ji1udd/VFO-Controller/Doc/Shop2906194(Not Available Now)_SwitchLid_info2.jpg

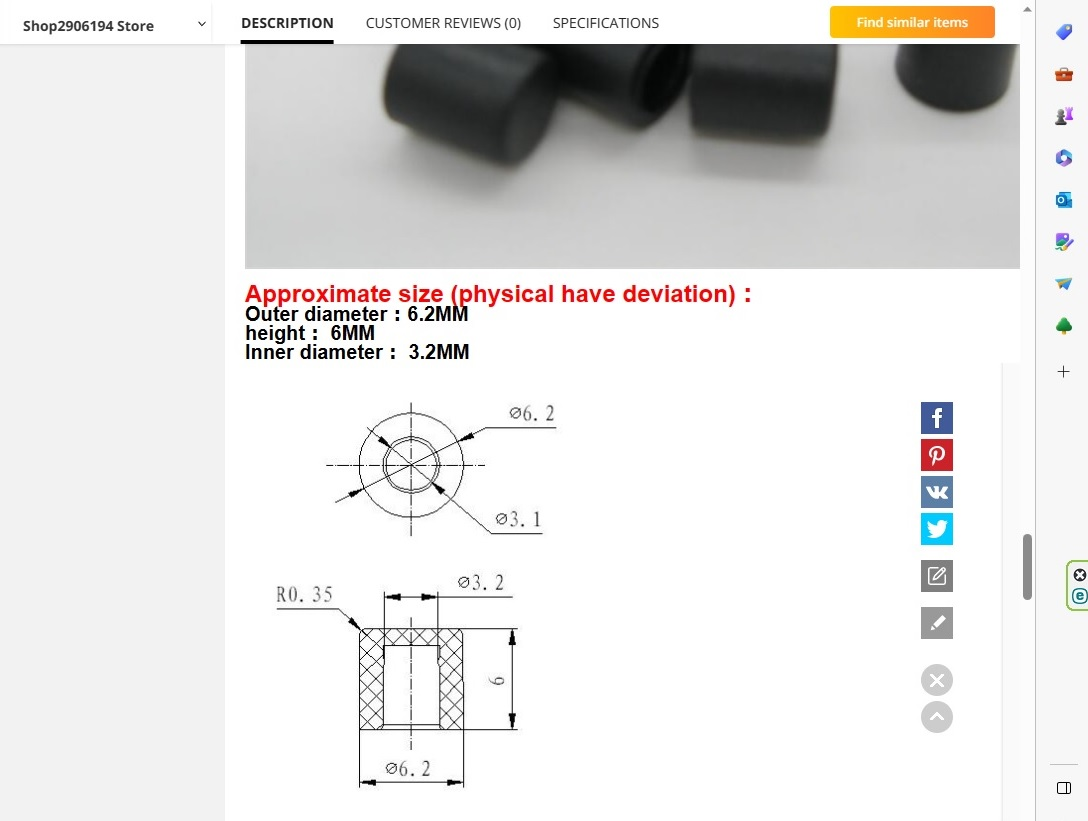
Doc/Shop2906194(Not Available Now)_SwitchLid_info2.jpg
